jaisor/ESP_LED_Controller/src/Device.cpp

#include <Arduino.h>
#include <functional>
#include <ArduinoLog.h>

#include "Device.h"

#if defined(OLED)
  #include <Adafruit_SSD1306.h>
  #include <Adafruit_GFX.h>
  #include <Wire.h>
#endif

int width = 72;
int height = 40;
int xOffset = 28; // = (132-w)/2
int yOffset = 24; // = (64-h)/2

static const char* deviceStateToString(DeviceState state) {
  switch (state) {
    case DeviceState::INITIALIZING:    return "INITIALIZING";
    case DeviceState::WIFI_AP_CREATED:  return "WIFI_AP_CREATED";
    case DeviceState::WIFI_CONNECTED:   return "WIFI_CONNECTED";
    case DeviceState::WIFI_OFFLINE:     return "WIFI_OFFLINE";
    default:                           return "UNKNOWN";
  }
}

CDevice::CDevice() {

  _state = DeviceState::INITIALIZING;
  tMillisUp = millis();

  #if defined(CONFIG_IDF_TARGET_ESP32C3) && defined(OLED)
    // ESP32C3 uses GPIO 5=SDA, GPIO 6=SCL - see https://wiki.seeedstudio.com/XIAO_ESP32C3_Getting_Started/
    Wire.begin(GPIO_NUM_5, GPIO_NUM_6);
    Wire.setClock(400000); // 400kHz I2C
    delay(100);
    
    _display = new Adafruit_SSD1306(128, 64, &Wire, -1);
    if(!_display->begin(SSD1306_SWITCHCAPVCC, OLED_I2C_ID)) {
        Log.errorln("SSD1306 OLED initialization failed with ID %x", OLED_I2C_ID);
    } else {
        Log.infoln("OLED initialized successfully");
        _display->clearDisplay();
        _display->setTextColor(SSD1306_WHITE);
        _display->setTextSize(1);
        _display->display();
    }
    
    // Create virtual canvas (128x40)
    virtualCanvas = new GFXcanvas1(VIRTUAL_WIDTH, VIRTUAL_HEIGHT);
    virtualCanvas->fillScreen(0); // Clear to black
    virtualCanvas->setTextColor(1); // White text
    
    virtualCanvas->setTextSize(1);
    virtualCanvas->setCursor(0, 10);
    virtualCanvas->print("Init...");
    
    // Initialize scrolling
    scrollOffset = 0;
    scrollDirection = 1; // 1 = right, -1 = left
    lastScrollTime = millis();
    scrollPaused = true; // Start with a pause
    pauseStartTime = millis();
    contentWidth = 0;
    scrollingEnabled = false;
    lastTimeUpdate = 0; // Force initial time update
    showingTempMessage = false;
    tempMessageEndTime = 0;
    
    // Calculate content bounds
    updateContentBounds();
    
    tMillisDisplayToggle = millis();
    displayToggleState = false;
    wifiConnected = false;
    strcpy(wifiSSID, "");
    strcpy(wifiIP, "");
  #endif


  Log.infoln(F("Device initialized"));
}

void CDevice::setState(DeviceState state) {
  if (_state != state) {
    Log.infoln("Device state: %s -> %s", deviceStateToString(_state), deviceStateToString(state));
    _state = state;
  }
}

CDevice::~CDevice() { 
#ifdef OLED
  if (virtualCanvas) {
    delete virtualCanvas;
  }
  if (_display) {
    delete _display;
  }
#endif
  Log.noticeln(F("Device destroyed"));
}

void CDevice::loop() {
  #ifdef OLED
  #ifdef CONFIG_IDF_TARGET_ESP32C3

  // Check if temporary message has expired
  if (showingTempMessage && millis() >= tempMessageEndTime) {
    showingTempMessage = false;
    lastTimeUpdate = 0; // Force time update
  }

  // Update time display once per minute (60000 ms) if not showing temp message
  if (_state == DeviceState::WIFI_CONNECTED && !showingTempMessage && millis() - lastTimeUpdate >= 60000) {
    struct tm timeinfo;
    lastTimeUpdate = millis();
    virtualCanvas->fillScreen(0);
      
    if (getLocalTime(&timeinfo, 100)) { // Short timeout to avoid blocking when NTP is unavailable  
      virtualCanvas->setTextColor(1); // White text
      virtualCanvas->setTextSize(2);
      
      // Format time as HH:MM AM/PM
      int hour12 = timeinfo.tm_hour % 12;
      if (hour12 == 0) hour12 = 12; // Convert 0 to 12 for 12-hour format
      
      char timeStr[16];
      snprintf(timeStr, sizeof(timeStr), "%02d:%02d", hour12, timeinfo.tm_min);
      int16_t textWidth = strlen(timeStr) * 12;
      
      virtualCanvas->setCursor((72 - textWidth) / 2, 0);
      virtualCanvas->print(timeStr);
      virtualCanvas->setCursor(72 / 2 - 16, 16);
      virtualCanvas->print((timeinfo.tm_hour >= 12) ? "PM" : "AM");
    } else {
      Log.warningln("Failed to get local time for display update");
    }
    // Update content bounds after drawing
    updateContentBounds();
  }
  
  // Update scroll position every 50ms
  if (millis() - lastScrollTime >= 50) {
    lastScrollTime = millis();
    
    // Only scroll if content extends beyond visible area
    if (scrollingEnabled) {
      // Check if we're in a pause state
      if (scrollPaused) {
        if (millis() - pauseStartTime >= SCROLL_PAUSE_MS) {
          scrollPaused = false; // Resume scrolling
        }
      } else {
        // Update scroll offset
        scrollOffset += scrollDirection;
        
        // Calculate max scroll based on actual content width
        int16_t maxScroll = contentWidth - OLED_SCREEN_WIDTH;
        if (maxScroll < 0) maxScroll = 0;
        
        // Check boundaries and start pause
        if (scrollOffset >= maxScroll) {
          scrollOffset = maxScroll;
          scrollDirection = -1;
          scrollPaused = true;
          pauseStartTime = millis();
        } else if (scrollOffset <= 0) {
          scrollOffset = 0;
          scrollDirection = 1;
          scrollPaused = true;
          pauseStartTime = millis();
        }
      }
    }
    
    // Clear hardware display
    _display->clearDisplay();
    
    // Copy visible portion of virtual canvas to hardware display
    // The virtual canvas is 128x40, we're viewing a 72x40 window
    // Position it at 28,24 on the 128x64 hardware display
    for (int16_t y = 0; y < VIRTUAL_HEIGHT && y < OLED_SCREEN_HEIGHT; y++) {
      for (int16_t x = 0; x < OLED_SCREEN_WIDTH; x++) {
        // Get pixel from virtual canvas at scrolled position
        int16_t virtualX = x + scrollOffset;
        if (virtualX >= 0 && virtualX < VIRTUAL_WIDTH) {
          uint16_t pixel = virtualCanvas->getPixel(virtualX, y);
          if (pixel) {
            _display->drawPixel(HARDWARE_X_OFFSET + x, HARDWARE_Y_OFFSET + y, SSD1306_WHITE);
          }
        }
      }
    }
    
    // Draw border for reference
    //_display->drawRect(HARDWARE_X_OFFSET, HARDWARE_Y_OFFSET, OLED_SCREEN_WIDTH, OLED_SCREEN_HEIGHT, SSD1306_WHITE);
    
    _display->display();
  }
  
  #endif
  #endif
}

#ifdef OLED
void CDevice::updateContentBounds() {
  #ifdef CONFIG_IDF_TARGET_ESP32C3
  if (!virtualCanvas) return;
  
  // Scan virtual canvas to find rightmost occupied pixel
  contentWidth = 0;
  
  for (int16_t x = VIRTUAL_WIDTH - 1; x >= 0; x--) {
    bool columnHasContent = false;
    for (int16_t y = 0; y < VIRTUAL_HEIGHT; y++) {
      if (virtualCanvas->getPixel(x, y)) {
        columnHasContent = true;
        break;
      }
    }
    if (columnHasContent) {
      contentWidth = x + 1; // +1 because we want the width, not the index
      break;
    }
  }
  
  // Enable scrolling only if content extends beyond visible area (72 pixels)
  scrollingEnabled = (contentWidth > OLED_SCREEN_WIDTH);
  
  // Reset scroll position if scrolling is disabled
  if (!scrollingEnabled) {
    scrollOffset = 0;
  }
  
  Log.infoln("Content width: %d, scrolling: %s", contentWidth, scrollingEnabled ? "enabled" : "disabled");
  #endif
}

void CDevice::displayTemporaryMessage(const char* message, unsigned long durationMs) {
  #ifdef CONFIG_IDF_TARGET_ESP32C3
  if (!virtualCanvas) return;
  
  // Clear and draw message
  virtualCanvas->fillScreen(0);
  virtualCanvas->setTextColor(1);
  virtualCanvas->setTextSize(2);
  
  virtualCanvas->setCursor(0, 10);
  virtualCanvas->print(message);
  
  // Update content bounds
  updateContentBounds();
  
  // Set temp message tracking
  showingTempMessage = true;
  tempMessageEndTime = millis() + durationMs;
  #endif
}
#endif
