jaisor/ESP_LED_Controller/src/migrator/min_spiffs_table.h

#pragma once

#include <stdint.h>

// framework-arduinoespressif32/tools/partitions/min_spiffs.csv as built by the framework's own
// gen_esp32part.py: 6 entries, then the MD5 entry over them. The rest of the 4KB sector is 0xFF.
// Regenerate with: python gen_esp32part.py min_spiffs.csv min_spiffs.bin (first 224 bytes)
//
//   nvs       data nvs       0x009000  0x005000
//   otadata   data ota       0x00e000  0x002000
//   app0      app  ota_0     0x010000  0x1e0000
//   app1      app  ota_1     0x1f0000  0x1e0000
//   spiffs    data spiffs    0x3d0000  0x020000
//   coredump  data coredump  0x3f0000  0x010000
static const uint8_t MIN_SPIFFS_TABLE[] = {
  0xaa, 0x50, 0x01, 0x02, 0x00, 0x90, 0x00, 0x00, 0x00, 0x50, 0x00, 0x00, 0x6e, 0x76, 0x73, 0x00,
  0x00, 0x00, 0x00, 0x00, 0x00, 0x00, 0x00, 0x00, 0x00, 0x00, 0x00, 0x00, 0x00, 0x00, 0x00, 0x00,
  0xaa, 0x50, 0x01, 0x00, 0x00, 0xe0, 0x00, 0x00, 0x00, 0x20, 0x00, 0x00, 0x6f, 0x74, 0x61, 0x64,
  0x61, 0x74, 0x61, 0x00, 0x00, 0x00, 0x00, 0x00, 0x00, 0x00, 0x00, 0x00, 0x00, 0x00, 0x00, 0x00,
  0xaa, 0x50, 0x00, 0x10, 0x00, 0x00, 0x01, 0x00, 0x00, 0x00, 0x1e, 0x00, 0x61, 0x70, 0x70, 0x30,
  0x00, 0x00, 0x00, 0x00, 0x00, 0x00, 0x00, 0x00, 0x00, 0x00, 0x00, 0x00, 0x00, 0x00, 0x00, 0x00,
  0xaa, 0x50, 0x00, 0x11, 0x00, 0x00, 0x1f, 0x00, 0x00, 0x00, 0x1e, 0x00, 0x61, 0x70, 0x70, 0x31,
  0x00, 0x00, 0x00, 0x00, 0x00, 0x00, 0x00, 0x00, 0x00, 0x00, 0x00, 0x00, 0x00, 0x00, 0x00, 0x00,
  0xaa, 0x50, 0x01, 0x82, 0x00, 0x00, 0x3d, 0x00, 0x00, 0x00, 0x02, 0x00, 0x73, 0x70, 0x69, 0x66,
  0x66, 0x73, 0x00, 0x00, 0x00, 0x00, 0x00, 0x00, 0x00, 0x00, 0x00, 0x00, 0x00, 0x00, 0x00, 0x00,
  0xaa, 0x50, 0x01, 0x03, 0x00, 0x00, 0x3f, 0x00, 0x00, 0x00, 0x01, 0x00, 0x63, 0x6f, 0x72, 0x65,
  0x64, 0x75, 0x6d, 0x70, 0x00, 0x00, 0x00, 0x00, 0x00, 0x00, 0x00, 0x00, 0x00, 0x00, 0x00, 0x00,
  0xeb, 0xeb, 0xff, 0xff, 0xff, 0xff, 0xff, 0xff, 0xff, 0xff, 0xff, 0xff, 0xff, 0xff, 0xff, 0xff,
  0xb4, 0x35, 0x13, 0xb1, 0x22, 0xc4, 0x18, 0x73, 0xa9, 0x01, 0x0b, 0x82, 0xec, 0x3a, 0x25, 0xbd,
};
