jaisor/ESP_LED_Controller/src/modes/ColorSplitMode.h

#pragma once

#include "BaseMode.h"

class CColorSplitMode : public CBaseMode {

private:
  uint8_t startIndex = 0;
  const float increment;
  //const TProgmemRGBPalette16& palette1, palette2;
  const TBlendType blendType;
  const unsigned long delay;
  const uint16_t splitAt;

public:
	CColorSplitMode(const uint16_t numLeds, const uint16_t splitAt, const String name);
  virtual void draw(CRGB *leds);
};
