jaisor/ESP_LED_Controller/src/modes/SlavaUkrainiRingMode.h

#pragma once

#include <vector>
#include "BaseMode.h"

class CSlavaUkrainiRingMode : public CBaseMode {

private:
    uint8_t startIndex = 0;
    const float increment;
    const TBlendType blendType;
    const unsigned long delay;
    std::vector<CLEDSegment> segments;

public:
	CSlavaUkrainiRingMode(const uint16_t numLeds, const uint16_t numLedsOutter, const String name);
    virtual void draw(CRGB *leds);
};
