jaisor/ESP_LED_Controller/src/wifi/HTMLAssets.h

#pragma once

#include <Arduino.h>

extern const char htmlTop[];
extern const char htmlBottom[];
extern const char htmlWifi[];
extern const char htmlDevice[];
extern const char htmlLed[];
extern const char htmlModes[];
extern const char htmlMain[];

extern const char cssPico[];
